webdidacticat/weatherpi/img/photo_2022-05-09_13-50-47.jpg

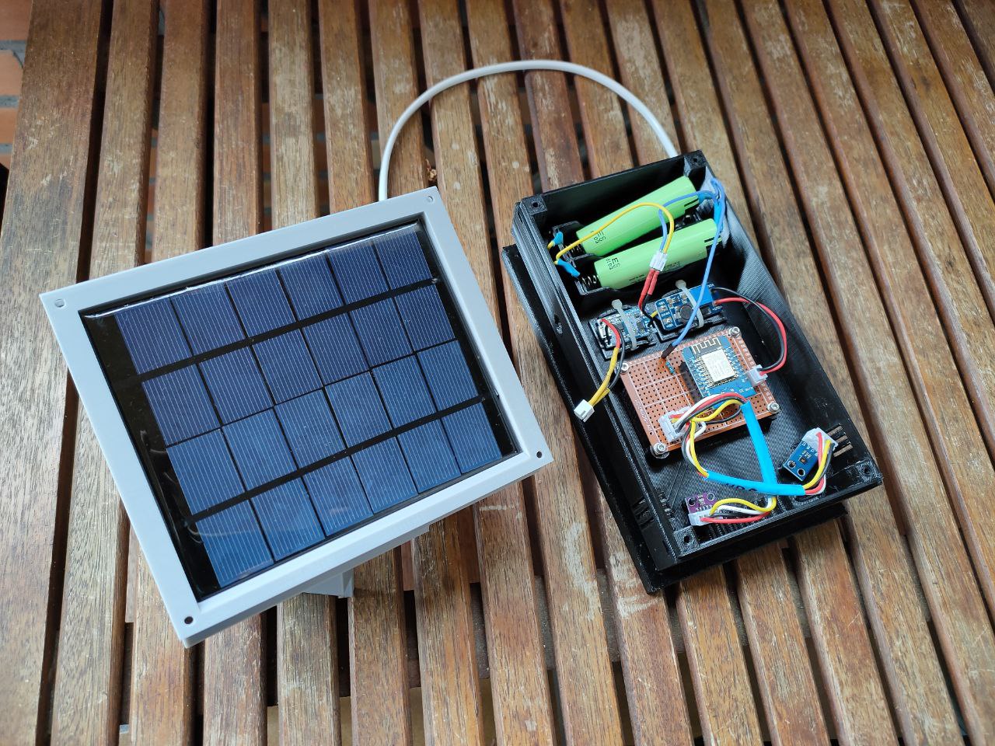
img/photo_2022-05-09_13-50-47.jpg
