webdidacticat/weatherpi/weather.iot/public_html/img/img1.jpg

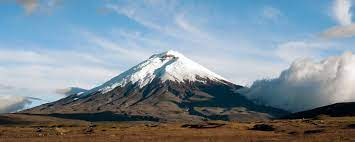
weather.iot/public_html/img/img1.jpg
