webdidacticat/weatherpi/weather.iot/public_html/img/img2.jpg

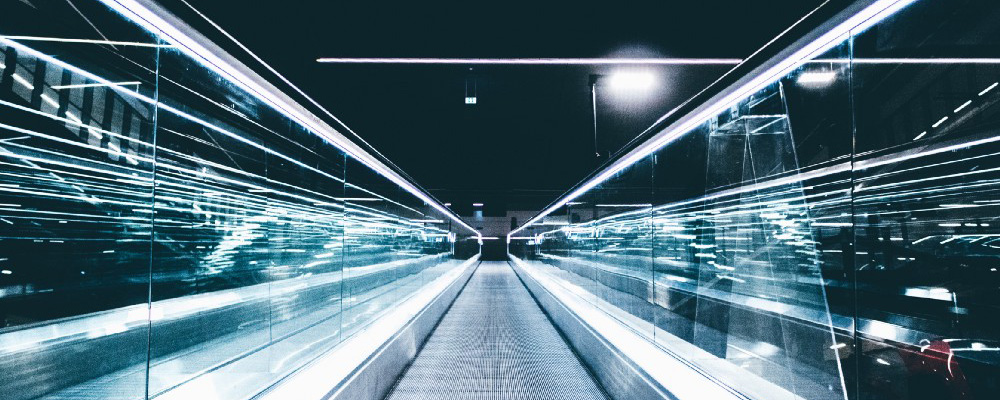
weather.iot/public_html/img/img2.jpg
