webdidacticat/weatherpi/weather.iot/public_html/img/img3.jpg

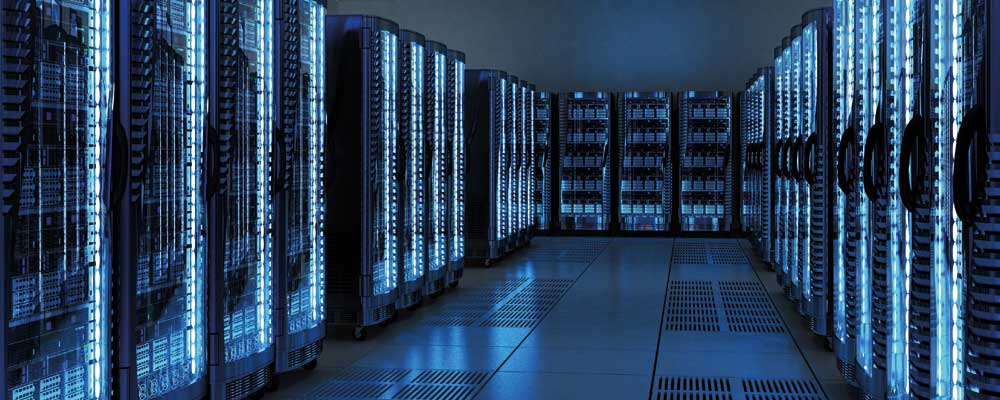
weather.iot/public_html/img/img3.jpg
