webdidacticat/weatherpi/weather.iot/public_html/img/img4.jpg

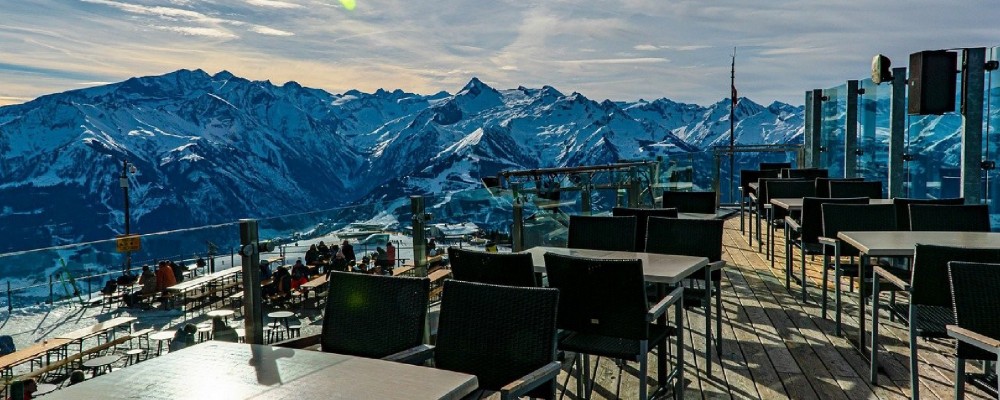
weather.iot/public_html/img/img4.jpg
